grimreeper132/Talking-Ham/Schematics/Layout Scheen shots/RF-INP-001.png

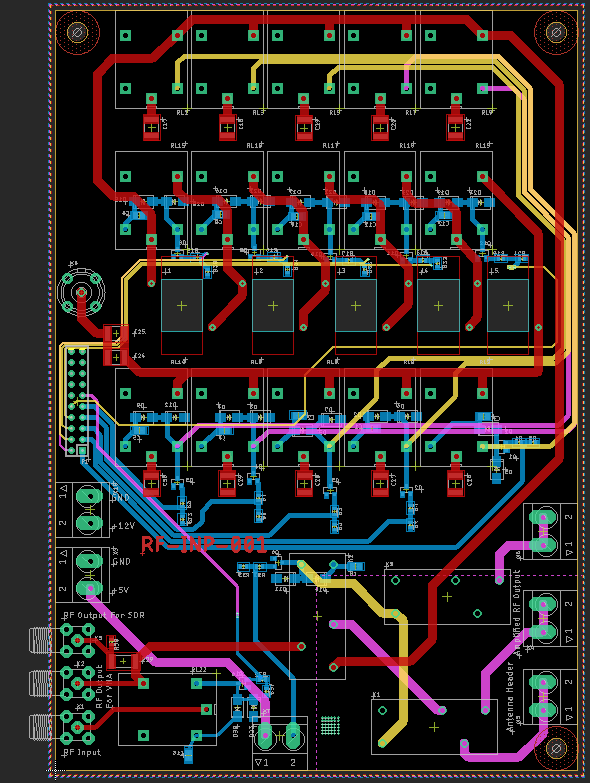
Schematics/Layout Scheen shots/RF-INP-001.png
