grimreeper132/Talking-Ham/Schematics/Layout Scheen shots/RF-OUT-001.png

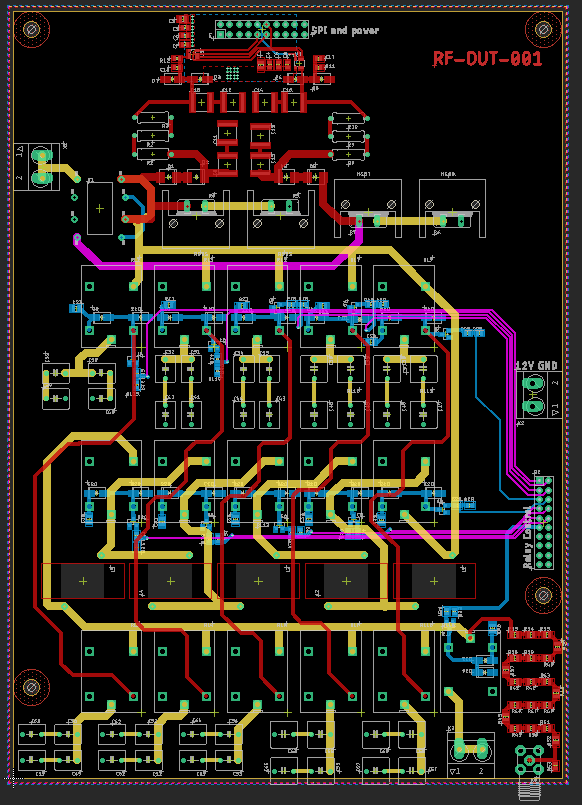
Schematics/Layout Scheen shots/RF-OUT-001.png
