grimreeper132/Talking-Ham/Schematics/Layout Scheen shots/RF-PWR-001.png

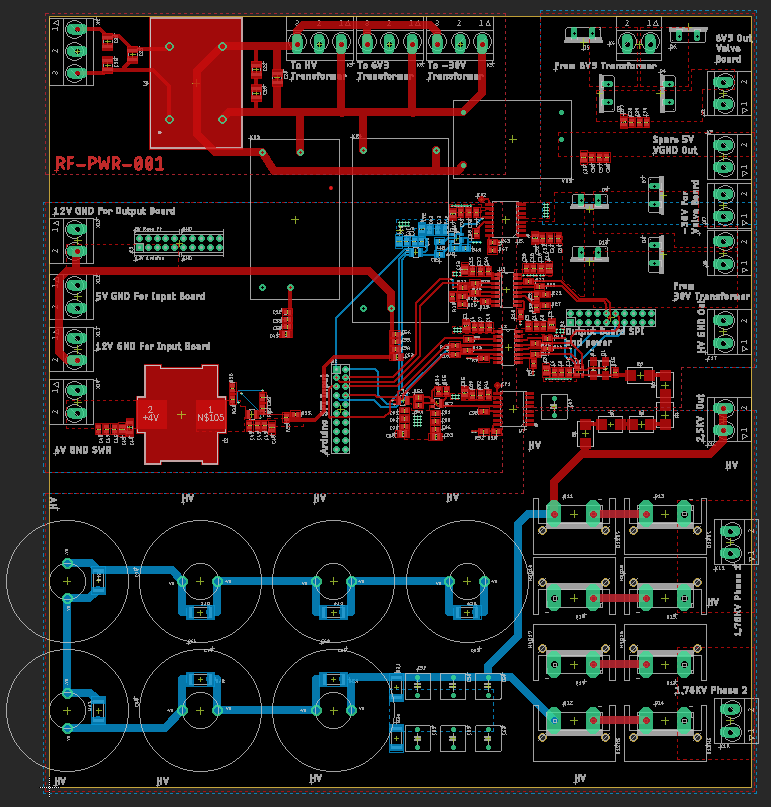
Schematics/Layout Scheen shots/RF-PWR-001.png
