grimreeper132/Talking-Ham/Schematics/Layout Scheen shots/RF-VAL-001 With Planes W Hole.png

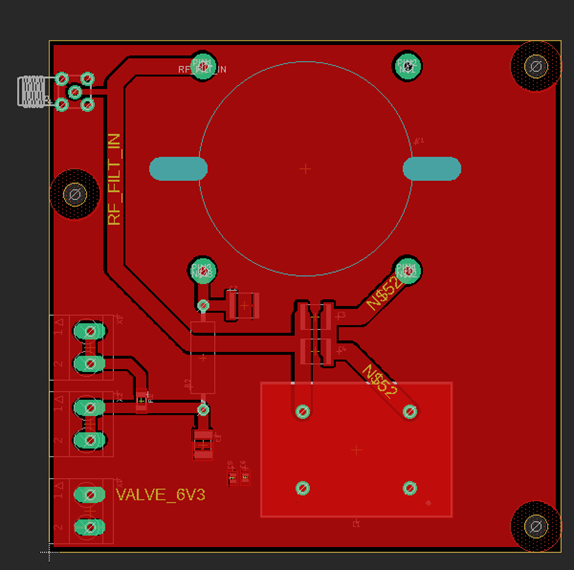
Schematics/Layout Scheen shots/RF-VAL-001 With Planes W Hole.png
