grimreeper132/Talking-Ham/Schematics/Layout Scheen shots/RF-VAL-001 With Planes.png

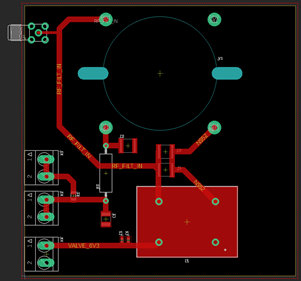
Schematics/Layout Scheen shots/RF-VAL-001 With Planes.png
